Twotoz/OpenPocket/display/amt630a-openpocket/src/registers.c

#include "amt630a.h"

// Values are independently transcribed from the AMT630A specification,
// public register documentation, and the 430D reference circuit. This table
// contains configuration data only; it is not derived from a firmware dump.
const __code register_write_t openpocket_registers[] = {
    {0xfd11, 0xff}, {0xfd12, 0xff}, {0xfd13, 0xff}, {0xfd19, 0x83},
    {0xfd0b, 0x40}, {0xfd0d, 0xf0}, {0xfd0e, 0x2c}, {0xfd0a, 0xa8},
    {0xfd0f, 0x09}, {0xfd14, 0x03}, {0xfd15, 0x02}, {0xfd10, 0x04},
    {0xfd16, 0x0a}, {0xfd17, 0x18}, {0xfd1a, 0x08},
    {0xfc00, 0x00},
    {0xfd34, 0x22}, {0xfd35, 0x22}, {0xfd36, 0x22}, {0xfd37, 0x22},
    {0xfd38, 0x22}, {0xfd39, 0x22}, {0xfd3a, 0x22}, {0xfd3b, 0x22},
    {0xfd3c, 0x22}, {0xfd3d, 0x22}, {0xfd3e, 0x22}, {0xfd3f, 0x22},
    {0xfd40, 0x22}, {0xfd41, 0x22}, {0xfd42, 0x22}, {0xfd43, 0x22},
    {0xfd50, 0x0f},
    {0xfe04, 0x30}, {0xfe05, 0x40}, {0xfe13, 0x1e}, {0xfe56, 0x00},
    {0xfe83, 0xfe}, {0xfeb5, 0x67}, {0xfeba, 0xff}, {0xfec9, 0x01},
    {0xfed9, 0x40}, {0xfedb, 0x00},
    // CVBS1: disable path, select input one, then enable. Snow-disable and
    // blue/background-substitution bits remain clear.
    {0xfed7, 0x00}, {0xfed8, 0x80}, {0xfedc, 0x00}, {0xfed7, 0x18},
    {0xfc90, 0x02},
    // NTSC/60-Hz 16:9 full-panel scaler.
    {0xfc91, 0x01}, {0xfc92, 0x00}, {0xfc93, 0x00},
    {0xfc94, 0x00}, {0xfc95, 0x00}, {0xfc96, 0x61}, {0xfc97, 0x08},
    {0xfc98, 0xc8}, {0xfc99, 0x03}, {0xfc9a, 0xe3}, {0xfc9b, 0x01},
    {0xfc9c, 0x00}, {0xfc9d, 0x00}, {0xfc9e, 0x44}, {0xfc9f, 0x00},
    {0xfca0, 0x43}, {0xfca1, 0x00}, {0xfca2, 0x8a}, {0xfca3, 0x01},
    {0xfca4, 0x07}, {0xfca5, 0x00}, {0xfca6, 0x09}, {0xfca7, 0x00},
    {0xfca8, 0x10}, {0xfca9, 0x00}, {0xfcaa, 0x10}, {0xfcab, 0x01},
    {0xfcac, 0x10}, {0xfcad, 0x00}, {0xfcae, 0x00}, {0xfcaf, 0x00},
    {0xfcb0, 0x00}, {0xfcb1, 0x14}, {0xfcb2, 0x00}, {0xfcb3, 0x00},
    {0xfcb4, 0x00}, {0xfcb5, 0x00}, {0xfcb6, 0x02},
    // PAL/50-Hz 16:9 full-panel scaler.
    {0xfcbd, 0x01}, {0xfcbe, 0x00}, {0xfcbf, 0x00},
    {0xfcc0, 0x00}, {0xfcc1, 0x00}, {0xfcc2, 0x5c}, {0xfcc3, 0x08},
    {0xfcc4, 0x66}, {0xfcc5, 0x04}, {0xfcc6, 0x36}, {0xfcc7, 0x02},
    {0xfcc8, 0x02}, {0xfcc9, 0x00}, {0xfcca, 0x36}, {0xfccb, 0x00},
    {0xfccc, 0x43}, {0xfccd, 0x00}, {0xfcce, 0x92}, {0xfccf, 0x01},
    {0xfcd0, 0x08}, {0xfcd1, 0x00}, {0xfcd2, 0x09}, {0xfcd3, 0x00},
    {0xfcd4, 0x0c}, {0xfcd5, 0x00}, {0xfcd6, 0x0f}, {0xfcd7, 0x01},
    {0xfcd8, 0x06}, {0xfcd9, 0x00}, {0xfcda, 0x00}, {0xfcdb, 0x00},
    {0xfcdc, 0x00}, {0xfcdd, 0x14}, {0xfcde, 0x00}, {0xfcdf, 0x00},
    {0xfce0, 0x00}, {0xfce1, 0x00}, {0xfce2, 0x02},
    {0xfcb7, 0x16}, {0xfcb8, 0x01}, {0xfcbb, 0x1c}, {0xfcbc, 0x01},
    {0xfce3, 0x01}, {0xfce4, 0x45},
};

const __code uint16_t openpocket_register_count =
    sizeof(openpocket_registers) / sizeof(openpocket_registers[0]);
